beniroquai/miniSPIM/IMAGES/IMG_20191011_124706.jpg

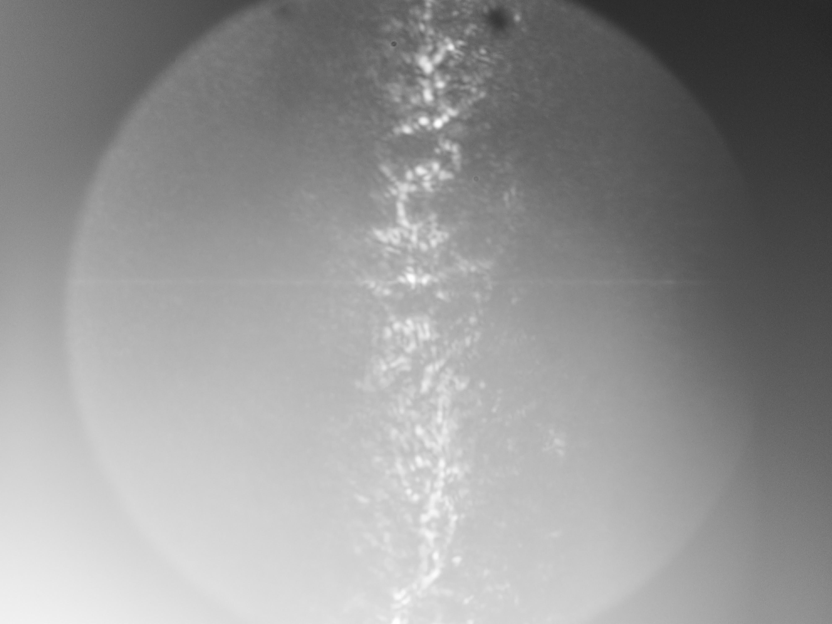
IMAGES/IMG_20191011_124706.jpg
