beniroquai/miniSPIM/IMAGES/IMG_20191014_163941.jpg

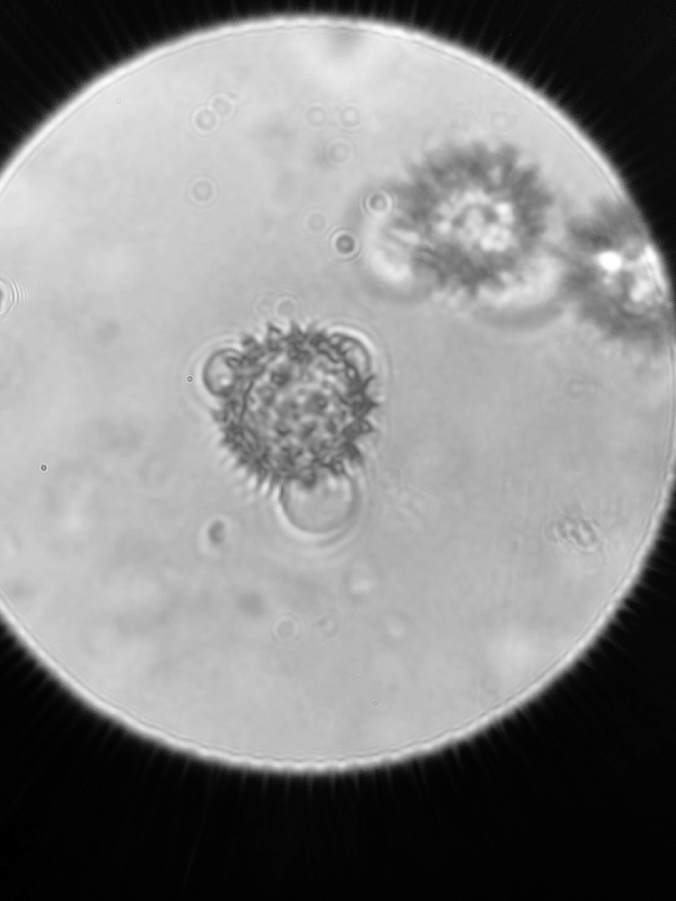
IMAGES/IMG_20191014_163941.jpg
