beniroquai/miniSPIM/IMAGES/IMG_20191014_164712.jpg

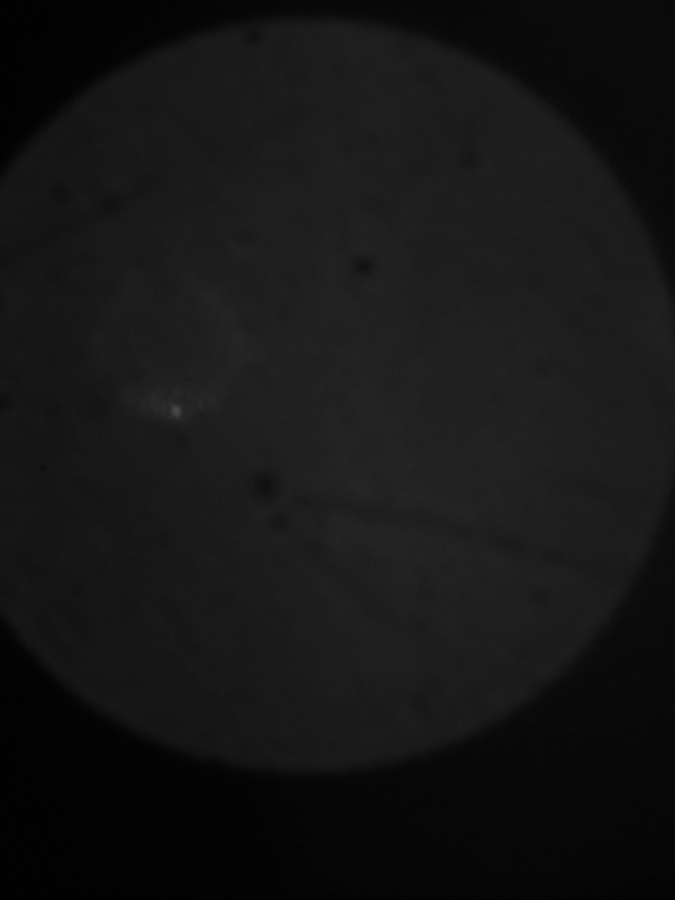
IMAGES/IMG_20191014_164712.jpg
