beniroquai/miniSPIM/IMAGES/IMG_20191015_173641.jpg

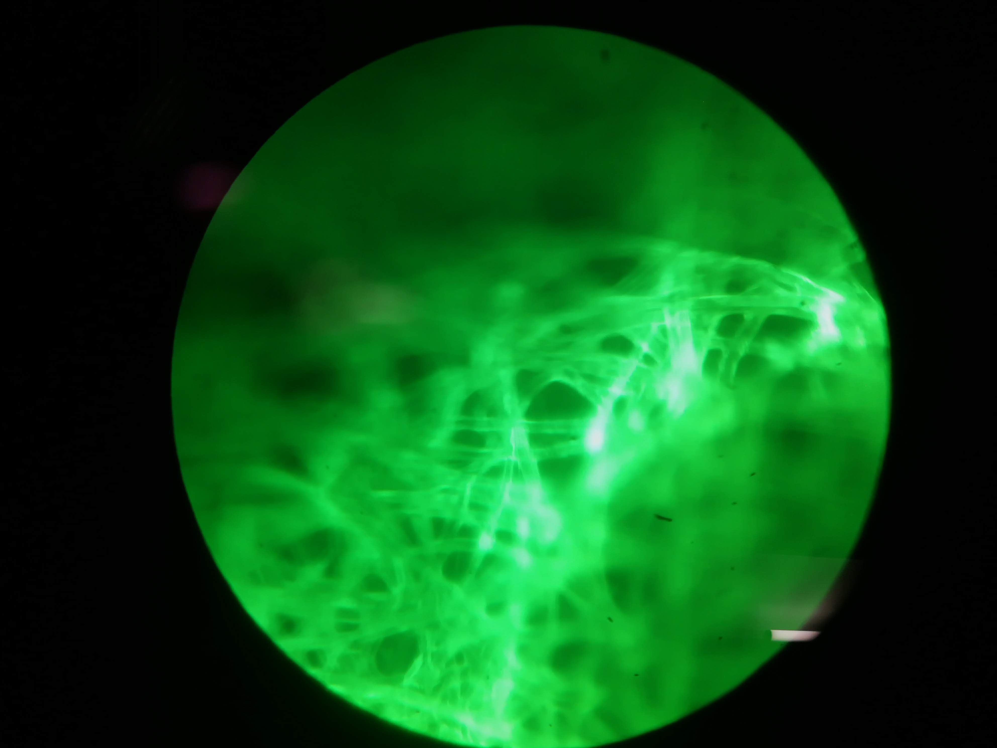
IMAGES/IMG_20191015_173641.jpg
