beniroquai/miniSPIM/IMAGES/miniSPIM_lenstissue.png

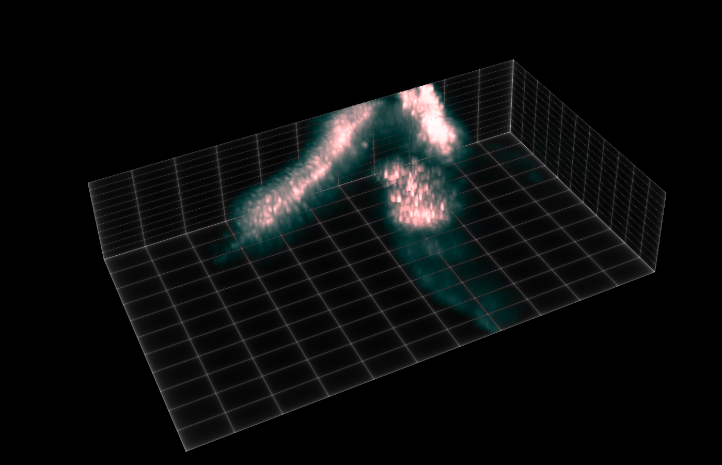
IMAGES/miniSPIM_lenstissue.png
