beniroquai/miniSPIM/ANDROID/miniSPIM-ANDROID/miniSPIM/.externalNativeBuild/ndkBuild/release/x86/ndkBuild_build_output.txt

rm -f /Users/Bene/Dropbox/Dokumente/OpticalDesign/Beamerscope/Android/BeamerscopeIlloptimization/holoscope/build/intermediates/ndkBuild/release/lib/x86/lib*.so
rm -f /Users/Bene/Dropbox/Dokumente/OpticalDesign/Beamerscope/Android/BeamerscopeIlloptimization/holoscope/build/intermediates/ndkBuild/release/lib/x86/gdbserver
rm -f /Users/Bene/Dropbox/Dokumente/OpticalDesign/Beamerscope/Android/BeamerscopeIlloptimization/holoscope/build/intermediates/ndkBuild/release/lib/x86/gdb.setup
mkdir -p /Users/Bene/Dropbox/Dokumente/OpticalDesign/Beamerscope/Android/BeamerscopeIlloptimization/holoscope/.externalNativeBuild/ndkBuild/release/obj/local/x86/objs/native_microscope
echo [x86] "Compile++      ": "native_microscope <= cvComplex.cpp"
/Users/Bene/Library/Android/sdk/ndk-bundle/toolchains/x86-4.9/prebuilt/darwin-x86_64/bin/i686-linux-android-g++ -MMD -MP -MF /Users/Bene/Dropbox/Dokumente/OpticalDesign/Beamerscope/Android/BeamerscopeIlloptimization/holoscope/.externalNativeBuild/ndkBuild/release/obj/local/x86/objs/native_microscope/cvComplex.o.d -ffunction-sections -funwind-tables -no-canonical-prefixes  -g -fstack-protector-strong -fno-exceptions -fno-rtti -O2 -DNDEBUG  -I"/Users/Bene/Android/opencv3/sdk/native/jni/include/opencv" -I"/Users/Bene/Android/opencv3/sdk/native/jni/include" -I/Users/Bene/Android/opencv3/sdk/native/jni/include/ -I/Users/Bene/Dropbox/Dokumente/OpticalDesign/Beamerscope/Android/BeamerscopeIlloptimization/holoscope/src/main/jni -I/Users/Bene/Library/Android/sdk/ndk-bundle/sources/cxx-stl/gnu-libstdc++/4.9/include -I/Users/Bene/Library/Android/sdk/ndk-bundle/sources/cxx-stl/gnu-libstdc++/4.9/libs/x86/include -I/Users/Bene/Library/Android/sdk/ndk-bundle/sources/cxx-stl/gnu-libstdc++/4.9/include/backward -I/Users/Bene/Dropbox/Dokumente/OpticalDesign/Beamerscope/Android/BeamerscopeIlloptimization/holoscope/src/main/jni -DANDROID -fPIC -DANDROID -fsigned-char -Wa,--noexecstack -Wformat -Werror=format-security    -frtti -fexceptions  -isystem /Users/Bene/Library/Android/sdk/ndk-bundle/platforms/android-19/arch-x86/usr/include -c  /Users/Bene/Dropbox/Dokumente/OpticalDesign/Beamerscope/Android/BeamerscopeIlloptimization/holoscope/src/main/jni/cvComplex.cpp -o /Users/Bene/Dropbox/Dokumente/OpticalDesign/Beamerscope/Android/BeamerscopeIlloptimization/holoscope/.externalNativeBuild/ndkBuild/release/obj/local/x86/objs/native_microscope/cvComplex.o 
echo [x86] "Compile++      ": "native_microscope <= common.cpp"
/Users/Bene/Library/Android/sdk/ndk-bundle/toolchains/x86-4.9/prebuilt/darwin-x86_64/bin/i686-linux-android-g++ -MMD -MP -MF /Users/Bene/Dropbox/Dokumente/OpticalDesign/Beamerscope/Android/BeamerscopeIlloptimization/holoscope/.externalNativeBuild/ndkBuild/release/obj/local/x86/objs/native_microscope/common.o.d -ffunction-sections -funwind-tables -no-canonical-prefixes  -g -fstack-protector-strong -fno-exceptions -fno-rtti -O2 -DNDEBUG  -I"/Users/Bene/Android/opencv3/sdk/native/jni/include/opencv" -I"/Users/Bene/Android/opencv3/sdk/native/jni/include" -I/Users/Bene/Android/opencv3/sdk/native/jni/include/ -I/Users/Bene/Dropbox/Dokumente/OpticalDesign/Beamerscope/Android/BeamerscopeIlloptimization/holoscope/src/main/jni -I/Users/Bene/Library/Android/sdk/ndk-bundle/sources/cxx-stl/gnu-libstdc++/4.9/include -I/Users/Bene/Library/Android/sdk/ndk-bundle/sources/cxx-stl/gnu-libstdc++/4.9/libs/x86/include -I/Users/Bene/Library/Android/sdk/ndk-bundle/sources/cxx-stl/gnu-libstdc++/4.9/include/backward -I/Users/Bene/Dropbox/Dokumente/OpticalDesign/Beamerscope/Android/BeamerscopeIlloptimization/holoscope/src/main/jni -DANDROID -fPIC -DANDROID -fsigned-char -Wa,--noexecstack -Wformat -Werror=format-security    -frtti -fexceptions  -isystem /Users/Bene/Library/Android/sdk/ndk-bundle/platforms/android-19/arch-x86/usr/include -c  /Users/Bene/Dropbox/Dokumente/OpticalDesign/Beamerscope/Android/BeamerscopeIlloptimization/holoscope/src/main/jni/common.cpp -o /Users/Bene/Dropbox/Dokumente/OpticalDesign/Beamerscope/Android/BeamerscopeIlloptimization/holoscope/.externalNativeBuild/ndkBuild/release/obj/local/x86/objs/native_microscope/common.o 
echo [x86] "Compile++      ": "native_microscope <= jni_qDPC.cpp"
/Users/Bene/Library/Android/sdk/ndk-bundle/toolchains/x86-4.9/prebuilt/darwin-x86_64/bin/i686-linux-android-g++ -MMD -MP -MF /Users/Bene/Dropbox/Dokumente/OpticalDesign/Beamerscope/Android/BeamerscopeIlloptimization/holoscope/.externalNativeBuild/ndkBuild/release/obj/local/x86/objs/native_microscope/jni_qDPC.o.d -ffunction-sections -funwind-tables -no-canonical-prefixes  -g -fstack-protector-strong -fno-exceptions -fno-rtti -O2 -DNDEBUG  -I"/Users/Bene/Android/opencv3/sdk/native/jni/include/opencv" -I"/Users/Bene/Android/opencv3/sdk/native/jni/include" -I/Users/Bene/Android/opencv3/sdk/native/jni/include/ -I/Users/Bene/Dropbox/Dokumente/OpticalDesign/Beamerscope/Android/BeamerscopeIlloptimization/holoscope/src/main/jni -I/Users/Bene/Library/Android/sdk/ndk-bundle/sources/cxx-stl/gnu-libstdc++/4.9/include -I/Users/Bene/Library/Android/sdk/ndk-bundle/sources/cxx-stl/gnu-libstdc++/4.9/libs/x86/include -I/Users/Bene/Library/Android/sdk/ndk-bundle/sources/cxx-stl/gnu-libstdc++/4.9/include/backward -I/Users/Bene/Dropbox/Dokumente/OpticalDesign/Beamerscope/Android/BeamerscopeIlloptimization/holoscope/src/main/jni -DANDROID -fPIC -DANDROID -fsigned-char -Wa,--noexecstack -Wformat -Werror=format-security    -frtti -fexceptions  -isystem /Users/Bene/Library/Android/sdk/ndk-bundle/platforms/android-19/arch-x86/usr/include -c  /Users/Bene/Dropbox/Dokumente/OpticalDesign/Beamerscope/Android/BeamerscopeIlloptimization/holoscope/src/main/jni/jni_qDPC.cpp -o /Users/Bene/Dropbox/Dokumente/OpticalDesign/Beamerscope/Android/BeamerscopeIlloptimization/holoscope/.externalNativeBuild/ndkBuild/release/obj/local/x86/objs/native_microscope/jni_qDPC.o 
echo [x86] "Compile++      ": "native_microscope <= jni_illpattern.cpp"
/Users/Bene/Library/Android/sdk/ndk-bundle/toolchains/x86-4.9/prebuilt/darwin-x86_64/bin/i686-linux-android-g++ -MMD -MP -MF /Users/Bene/Dropbox/Dokumente/OpticalDesign/Beamerscope/Android/BeamerscopeIlloptimization/holoscope/.externalNativeBuild/ndkBuild/release/obj/local/x86/objs/native_microscope/jni_illpattern.o.d -ffunction-sections -funwind-tables -no-canonical-prefixes  -g -fstack-protector-strong -fno-exceptions -fno-rtti -O2 -DNDEBUG  -I"/Users/Bene/Android/opencv3/sdk/native/jni/include/opencv" -I"/Users/Bene/Android/opencv3/sdk/native/jni/include" -I/Users/Bene/Android/opencv3/sdk/native/jni/include/ -I/Users/Bene/Dropbox/Dokumente/OpticalDesign/Beamerscope/Android/BeamerscopeIlloptimization/holoscope/src/main/jni -I/Users/Bene/Library/Android/sdk/ndk-bundle/sources/cxx-stl/gnu-libstdc++/4.9/include -I/Users/Bene/Library/Android/sdk/ndk-bundle/sources/cxx-stl/gnu-libstdc++/4.9/libs/x86/include -I/Users/Bene/Library/Android/sdk/ndk-bundle/sources/cxx-stl/gnu-libstdc++/4.9/include/backward -I/Users/Bene/Dropbox/Dokumente/OpticalDesign/Beamerscope/Android/BeamerscopeIlloptimization/holoscope/src/main/jni -DANDROID -fPIC -DANDROID -fsigned-char -Wa,--noexecstack -Wformat -Werror=format-security    -frtti -fexceptions  -isystem /Users/Bene/Library/Android/sdk/ndk-bundle/platforms/android-19/arch-x86/usr/include -c  /Users/Bene/Dropbox/Dokumente/OpticalDesign/Beamerscope/Android/BeamerscopeIlloptimization/holoscope/src/main/jni/jni_illpattern.cpp -o /Users/Bene/Dropbox/Dokumente/OpticalDesign/Beamerscope/Android/BeamerscopeIlloptimization/holoscope/.externalNativeBuild/ndkBuild/release/obj/local/x86/objs/native_microscope/jni_illpattern.o 
echo [x86] "Compile++      ": "native_microscope <= jni_illparameter.cpp"
/Users/Bene/Library/Android/sdk/ndk-bundle/toolchains/x86-4.9/prebuilt/darwin-x86_64/bin/i686-linux-android-g++ -MMD -MP -MF /Users/Bene/Dropbox/Dokumente/OpticalDesign/Beamerscope/Android/BeamerscopeIlloptimization/holoscope/.externalNativeBuild/ndkBuild/release/obj/local/x86/objs/native_microscope/jni_illparameter.o.d -ffunction-sections -funwind-tables -no-canonical-prefixes  -g -fstack-protector-strong -fno-exceptions -fno-rtti -O2 -DNDEBUG  -I"/Users/Bene/Android/opencv3/sdk/native/jni/include/opencv" -I"/Users/Bene/Android/opencv3/sdk/native/jni/include" -I/Users/Bene/Android/opencv3/sdk/native/jni/include/ -I/Users/Bene/Dropbox/Dokumente/OpticalDesign/Beamerscope/Android/BeamerscopeIlloptimization/holoscope/src/main/jni -I/Users/Bene/Library/Android/sdk/ndk-bundle/sources/cxx-stl/gnu-libstdc++/4.9/include -I/Users/Bene/Library/Android/sdk/ndk-bundle/sources/cxx-stl/gnu-libstdc++/4.9/libs/x86/include -I/Users/Bene/Library/Android/sdk/ndk-bundle/sources/cxx-stl/gnu-libstdc++/4.9/include/backward -I/Users/Bene/Dropbox/Dokumente/OpticalDesign/Beamerscope/Android/BeamerscopeIlloptimization/holoscope/src/main/jni -DANDROID -fPIC -DANDROID -fsigned-char -Wa,--noexecstack -Wformat -Werror=format-security    -frtti -fexceptions  -isystem /Users/Bene/Library/Android/sdk/ndk-bundle/platforms/android-19/arch-x86/usr/include -c  /Users/Bene/Dropbox/Dokumente/OpticalDesign/Beamerscope/Android/BeamerscopeIlloptimization/holoscope/src/main/jni/jni_illparameter.cpp -o /Users/Bene/Dropbox/Dokumente/OpticalDesign/Beamerscope/Android/BeamerscopeIlloptimization/holoscope/.externalNativeBuild/ndkBuild/release/obj/local/x86/objs/native_microscope/jni_illparameter.o 
mkdir -p /Users/Bene/Dropbox/Dokumente/OpticalDesign/Beamerscope/Android/BeamerscopeIlloptimization/holoscope/.externalNativeBuild/ndkBuild/release/obj/local/x86
echo [x86] "Prebuilt       ": "libopencv_java3.so <= /Users/Bene/Android/opencv3/sdk/native/jni/../libs/x86/"
cp -f /Users/Bene/Android/opencv3/sdk/native/jni/../libs/x86/libopencv_java3.so /Users/Bene/Dropbox/Dokumente/OpticalDesign/Beamerscope/Android/BeamerscopeIlloptimization/holoscope/.externalNativeBuild/ndkBuild/release/obj/local/x86/libopencv_java3.so
echo [x86] "SharedLibrary  ": "libnative_microscope.so"
/Users/Bene/Library/Android/sdk/ndk-bundle/toolchains/x86-4.9/prebuilt/darwin-x86_64/bin/i686-linux-android-g++ -Wl,-soname,libnative_microscope.so -shared --sysroot=/Users/Bene/Library/Android/sdk/ndk-bundle/platforms/android-19/arch-x86 /Users/Bene/Dropbox/Dokumente/OpticalDesign/Beamerscope/Android/BeamerscopeIlloptimization/holoscope/.externalNativeBuild/ndkBuild/release/obj/local/x86/objs/native_microscope/cvComplex.o /Users/Bene/Dropbox/Dokumente/OpticalDesign/Beamerscope/Android/BeamerscopeIlloptimization/holoscope/.externalNativeBuild/ndkBuild/release/obj/local/x86/objs/native_microscope/common.o /Users/Bene/Dropbox/Dokumente/OpticalDesign/Beamerscope/Android/BeamerscopeIlloptimization/holoscope/.externalNativeBuild/ndkBuild/release/obj/local/x86/objs/native_microscope/jni_qDPC.o /Users/Bene/Dropbox/Dokumente/OpticalDesign/Beamerscope/Android/BeamerscopeIlloptimization/holoscope/.externalNativeBuild/ndkBuild/release/obj/local/x86/objs/native_microscope/jni_illpattern.o /Users/Bene/Dropbox/Dokumente/OpticalDesign/Beamerscope/Android/BeamerscopeIlloptimization/holoscope/.externalNativeBuild/ndkBuild/release/obj/local/x86/objs/native_microscope/jni_illparameter.o /Users/Bene/Library/Android/sdk/ndk-bundle/sources/cxx-stl/gnu-libstdc++/4.9/libs/x86/libgnustl_static.a -lgcc /Users/Bene/Dropbox/Dokumente/OpticalDesign/Beamerscope/Android/BeamerscopeIlloptimization/holoscope/.externalNativeBuild/ndkBuild/release/obj/local/x86/libopencv_java3.so -no-canonical-prefixes  -Wl,--build-id -Wl,--no-undefined -Wl,-z,noexecstack -Wl,-z,relro -Wl,-z,now -Wl,--warn-shared-textrel -Wl,--fatal-warnings  -L/Users/Bene/Library/Android/sdk/ndk-bundle/platforms/android-19/arch-x86/usr/lib -llog -ldl -lc -lm -o /Users/Bene/Dropbox/Dokumente/OpticalDesign/Beamerscope/Android/BeamerscopeIlloptimization/holoscope/.externalNativeBuild/ndkBuild/release/obj/local/x86/libnative_microscope.so
mkdir -p /Users/Bene/Dropbox/Dokumente/OpticalDesign/Beamerscope/Android/BeamerscopeIlloptimization/holoscope/build/intermediates/ndkBuild/release/lib/x86
echo [x86] "Install        ": "libnative_microscope.so => /Users/Bene/Dropbox/Dokumente/OpticalDesign/Beamerscope/Android/BeamerscopeIlloptimization/holoscope/build/intermediates/ndkBuild/release/lib/x86/libnative_microscope.so"
install -p /Users/Bene/Dropbox/Dokumente/OpticalDesign/Beamerscope/Android/BeamerscopeIlloptimization/holoscope/.externalNativeBuild/ndkBuild/release/obj/local/x86/libnative_microscope.so /Users/Bene/Dropbox/Dokumente/OpticalDesign/Beamerscope/Android/BeamerscopeIlloptimization/holoscope/build/intermediates/ndkBuild/release/lib/x86/libnative_microscope.so
/Users/Bene/Library/Android/sdk/ndk-bundle/toolchains/x86-4.9/prebuilt/darwin-x86_64/bin/i686-linux-android-strip --strip-unneeded  /Users/Bene/Dropbox/Dokumente/OpticalDesign/Beamerscope/Android/BeamerscopeIlloptimization/holoscope/build/intermediates/ndkBuild/release/lib/x86/libnative_microscope.so
echo [x86] "Install        ": "libopencv_java3.so => /Users/Bene/Dropbox/Dokumente/OpticalDesign/Beamerscope/Android/BeamerscopeIlloptimization/holoscope/build/intermediates/ndkBuild/release/lib/x86/libopencv_java3.so"
install -p /Users/Bene/Dropbox/Dokumente/OpticalDesign/Beamerscope/Android/BeamerscopeIlloptimization/holoscope/.externalNativeBuild/ndkBuild/release/obj/local/x86/libopencv_java3.so /Users/Bene/Dropbox/Dokumente/OpticalDesign/Beamerscope/Android/BeamerscopeIlloptimization/holoscope/build/intermediates/ndkBuild/release/lib/x86/libopencv_java3.so
/Users/Bene/Library/Android/sdk/ndk-bundle/toolchains/x86-4.9/prebuilt/darwin-x86_64/bin/i686-linux-android-strip --strip-unneeded  /Users/Bene/Dropbox/Dokumente/OpticalDesign/Beamerscope/Android/BeamerscopeIlloptimization/holoscope/build/intermediates/ndkBuild/release/lib/x86/libopencv_java3.so
